tdaede/td-crt/td-rgb/td-rgb.kicad_pcb

## KiCad design td-rgb/td-rgb.kicad_pcb (2019-02-07)

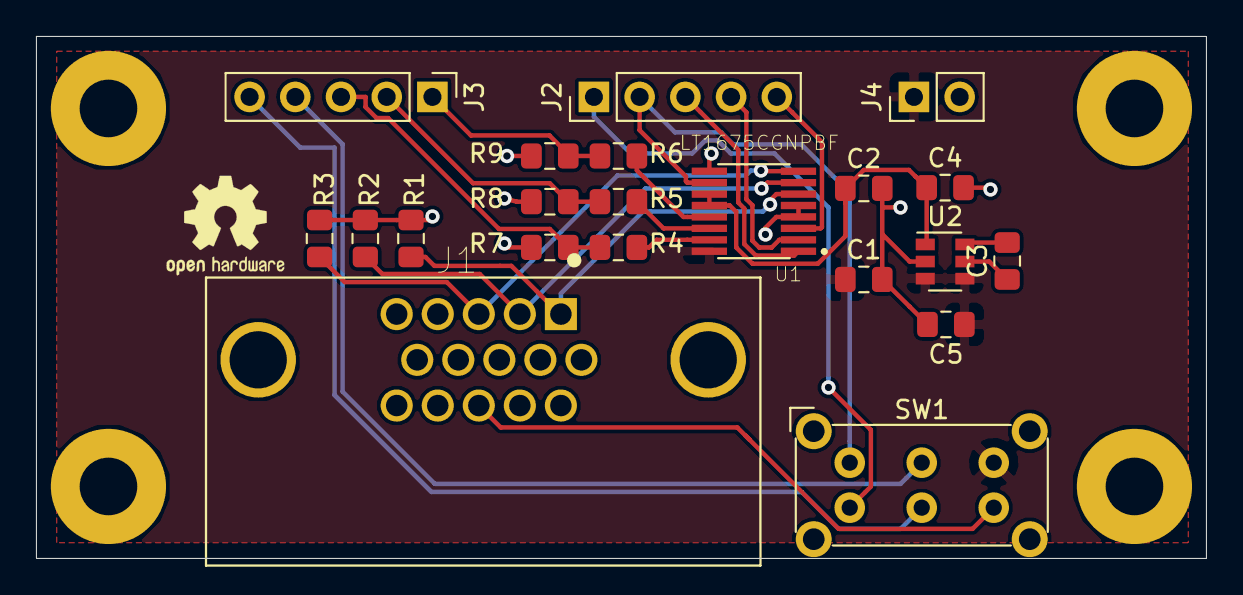
[picture p28: board td-rgb.kicad_pcb from above]

Board: 2 copper layers, 65.0 x 29.0 mm, 21 parts (0 on the bottom side), 22 nets.

Parts:
C1, C2: C; C_0805_2012Metric_Pad1.15x1.40mm_HandSolder
C3: 1uF; C_0805_2012Metric_Pad1.15x1.40mm_HandSolder
C4, C5: 2.2uF; C_0805_2012Metric_Pad1.15x1.40mm_HandSolder
J1: ICD15S13E4GV00LF; TE_1-1734530-1
J2, J3: Conn_01x05_Male; PinHeader_1x05_P2.54mm_Vertical
J4: Conn_01x02_Male; PinHeader_1x02_P2.54mm_Vertical
R1, R2, R3, R4, R5, R6, R7, R8, R9: 75; R_0805_2012Metric_Pad1.15x1.40mm_HandSolder
SW1: SW_DPDT_x2; SW_E-Switch_EG2219_DPDT_Angled
U1: LT1675CGNPBF; SOP63P600X172-16N
U2: LM2776; SOT-23-6

Connections:
+5V: C1.1, C5.1, J4.1, SW1.3, U1.16, U2.3, U2.4
-5V: C2.1, C4.1, U1.11, U1.12, U2.1
/blank_in: J2.2, SW1.1, U1.10
/blue: J1.3, R3.1, U1.8
/blue_in: J2.5, U1.3
/blue_out: J3.1, R6.1, R9.1
/csync_out: J3.5, SW1.5
/green: J1.2, R2.1, U1.7
/green_in: J2.4, U1.2
/green_out: J3.2, R5.1, R8.1
/red: J1.1, R1.1, U1.6
/red_in: J2.3, U1.1
/red_out: J3.3, R4.1, R7.1
GND: C1.2, C2.2, C4.2, C5.2, J1.5, J1.6, J1.7, J1.8, J4.2, R1.2, R2.2, R3.2, R7.2, R8.2, R9.2, U1.4, U1.5, U1.9, U2.2
unnamed: C3.1, U2.5
unnamed: C3.2, U2.6
unnamed: J1.13, SW1.6
unnamed: J2.1, SW1.4
unnamed: J3.4, SW1.2
unnamed: R4.2, U1.15
unnamed: R5.2, U1.14
unnamed: R6.2, U1.13
